oskar-fornander/DEC-HEX-Converter/model_a/images/a_pcb_front.png

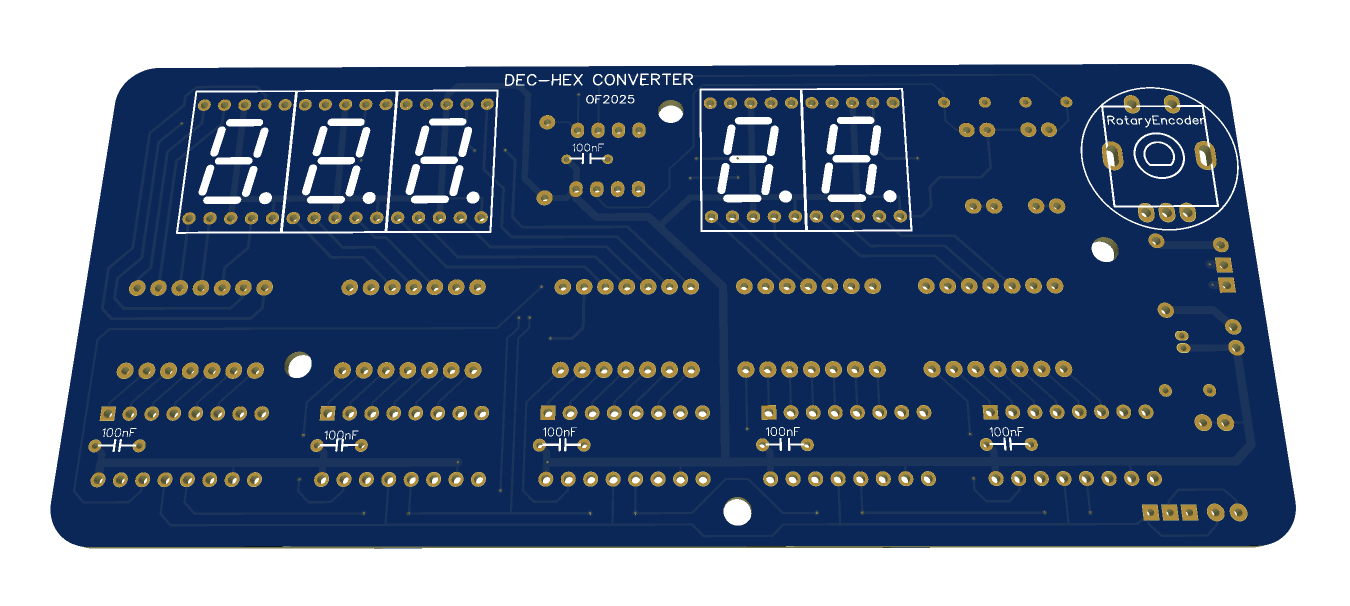
model_a/images/a_pcb_front.png
