oskar-fornander/DEC-HEX-Converter/model_a/images/DEC-HEX-Converter_A_02.jpg

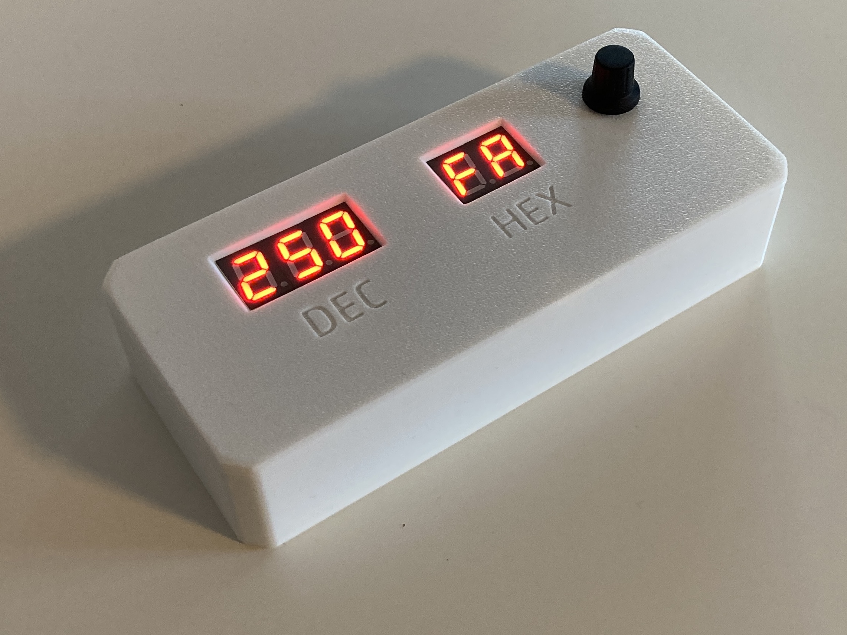
model_a/images/DEC-HEX-Converter_A_02.jpg
