oskar-fornander/DEC-HEX-Converter/model_a/images/DEC-HEX-Converter_A_03.jpg

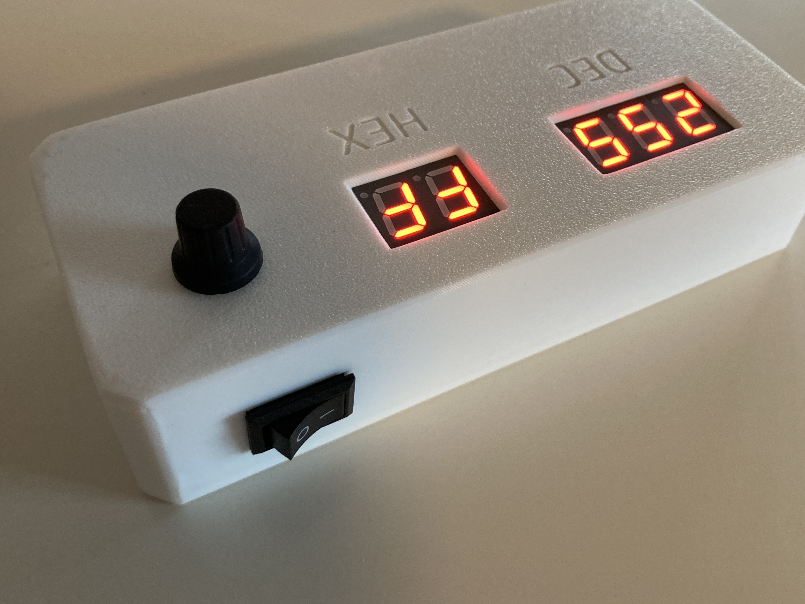
model_a/images/DEC-HEX-Converter_A_03.jpg
