oskar-fornander/DEC-HEX-Converter/model_a/images/DEC-HEX-Converter_A_04.JPG

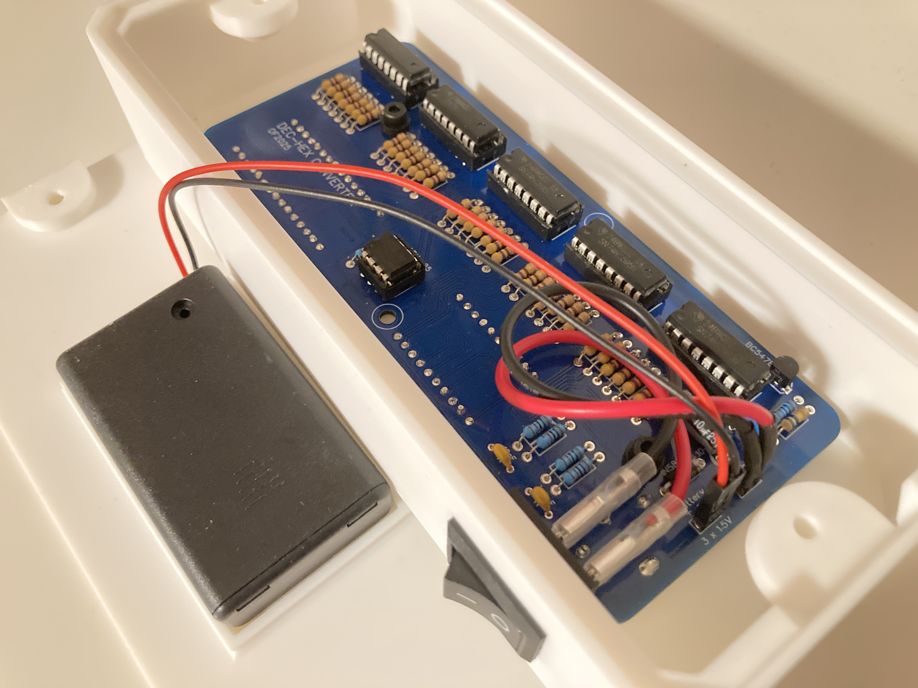
model_a/images/DEC-HEX-Converter_A_04.JPG
