oskar-fornander/DEC-HEX-Converter/model_b/images/DEC-HEX-Converter_B_03.jpg

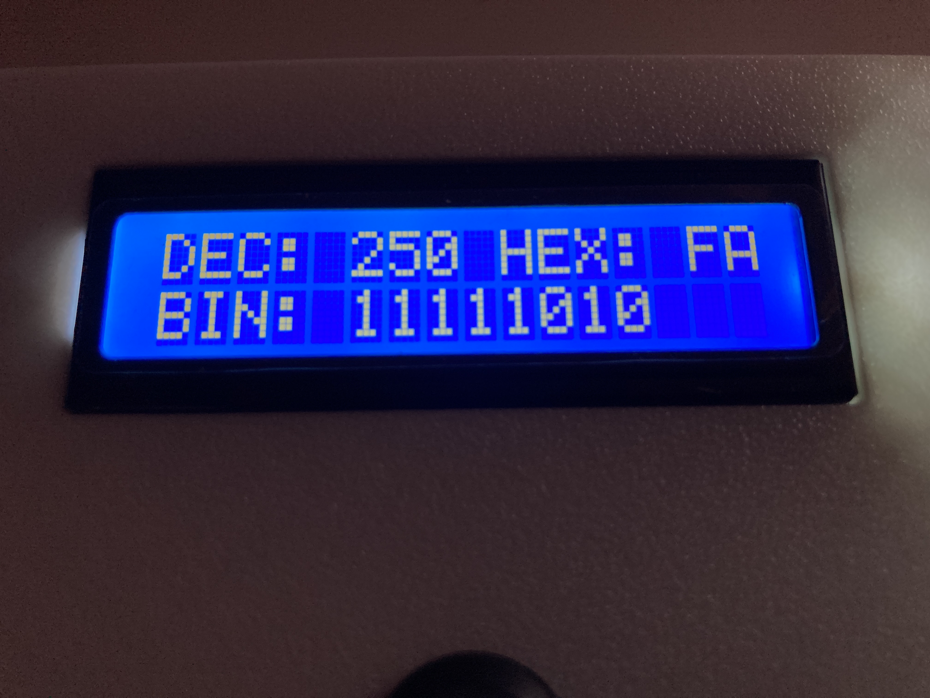
model_b/images/DEC-HEX-Converter_B_03.jpg
