oskar-fornander/DEC-HEX-Converter/model_b/images/DEC-HEX-Converter_B_05.jpg

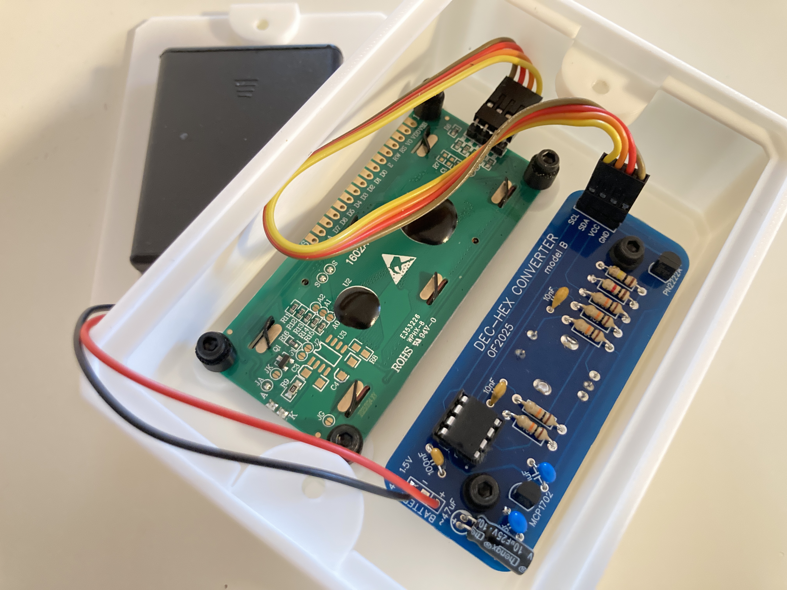
model_b/images/DEC-HEX-Converter_B_05.jpg
