oskar-fornander/DEC-HEX-Converter/qr_github.png

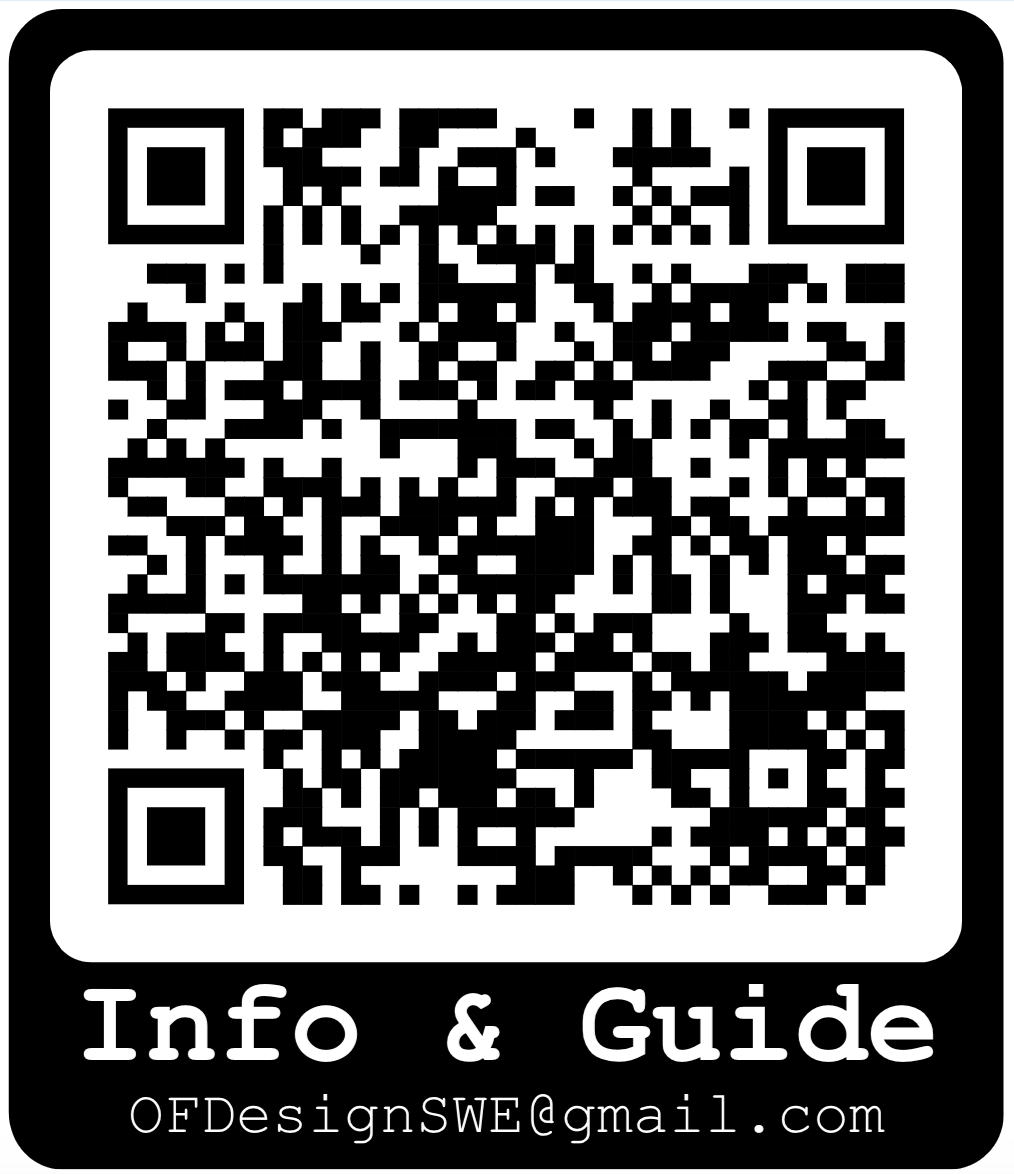
qr_github.png
